token2/openT2OTP/firmware/test/kat.c

/* SPDX-License-Identifier: MIT
 * Copyright (c) 2020-2026 Token2 Sarl
 *
 * Part of openT2OTP - the open-source release of the firmware core that runs
 * Token2's programmable TOTP hardware tokens. See LICENSE and README.md.
 */
#include "sm4.h"
#include <stdio.h>
#include <string.h>
int main(void){
  /* GM/T 0002-2012 standard KAT */
  uint8_t key[16]={0x01,0x23,0x45,0x67,0x89,0xab,0xcd,0xef,0xfe,0xdc,0xba,0x98,0x76,0x54,0x32,0x10};
  uint8_t pt [16]={0x01,0x23,0x45,0x67,0x89,0xab,0xcd,0xef,0xfe,0xdc,0xba,0x98,0x76,0x54,0x32,0x10};
  uint8_t exp[16]={0x68,0x1e,0xdf,0x34,0xd2,0x06,0x96,0x5e,0x86,0xb3,0xe9,0x4f,0x53,0x6e,0x42,0x46};
  uint8_t ct[16]; sm4_ecb_encrypt(key,pt,ct,1);
  int ok=memcmp(ct,exp,16)==0;
  printf("SM4 GM/T 0002 KAT: %s\n", ok?"PASS":"FAIL");
  return ok?0:1;
}
